ZitaoTech/9981_BLE_USB_Keyboard_Pro/Gallery/Foto1.jpg

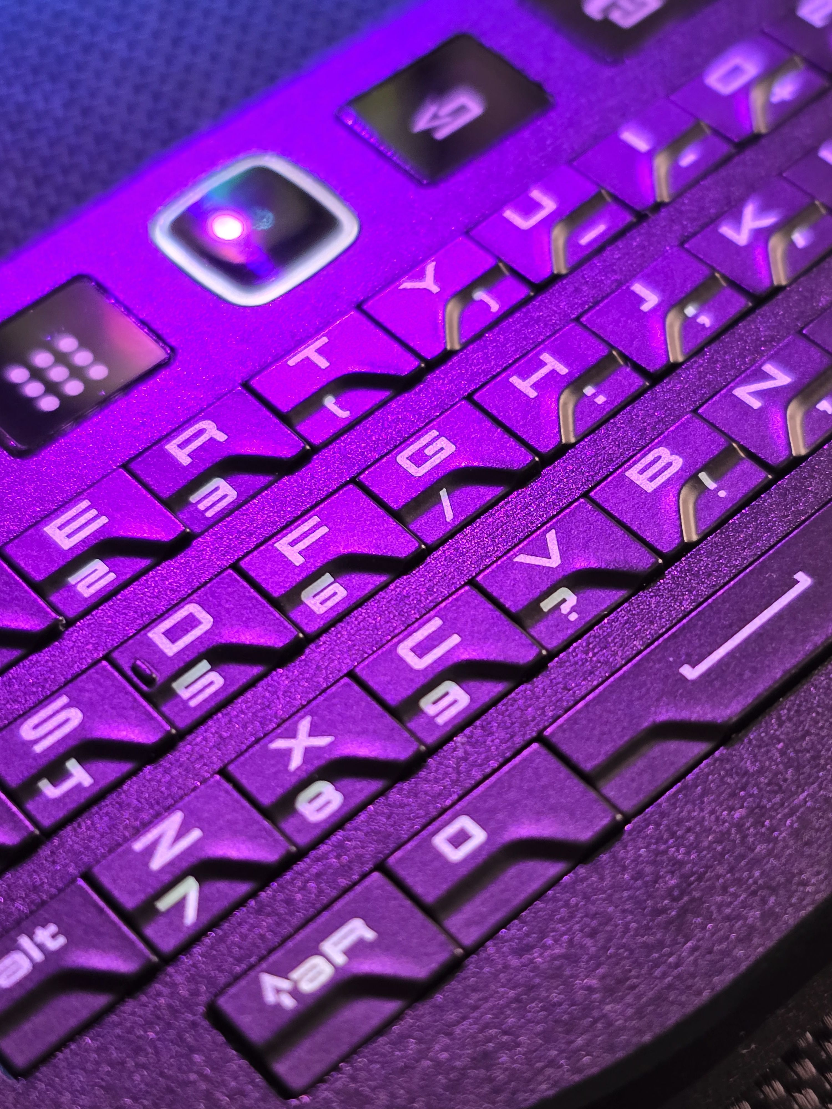
Gallery/Foto1.jpg
