ZitaoTech/9981_BLE_USB_Keyboard_Pro/Gallery/Foto3.jpg

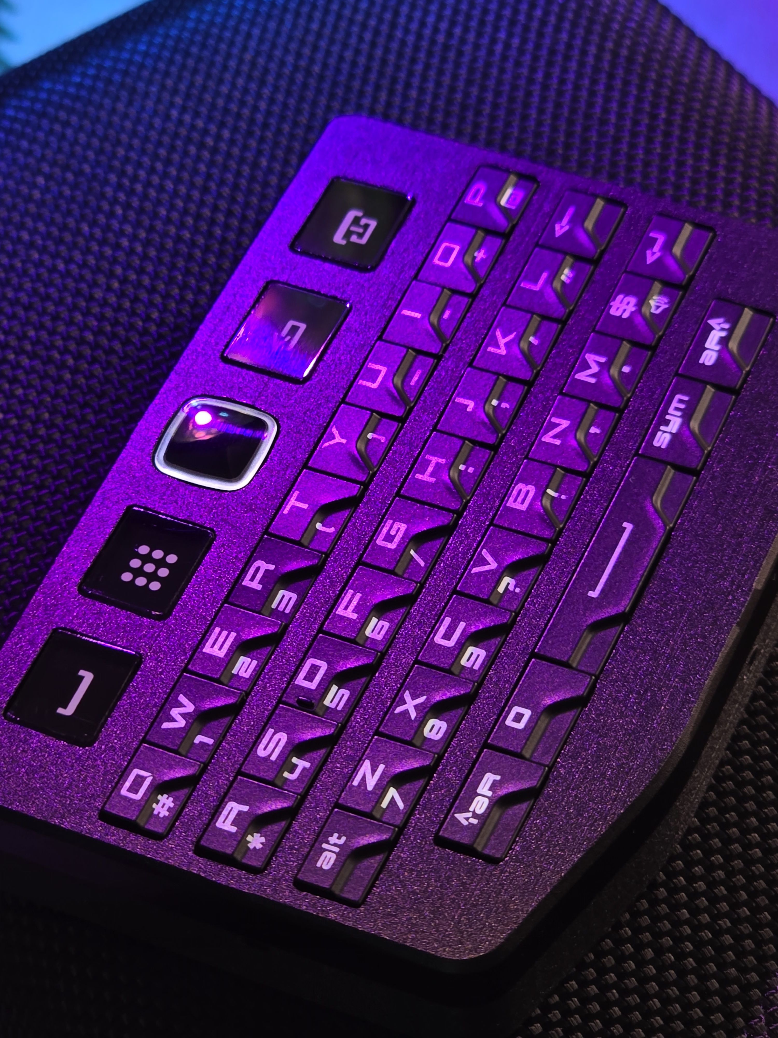
Gallery/Foto3.jpg
