ZitaoTech/9981_BLE_USB_Keyboard_Pro/Gallery/Foto4.jpg

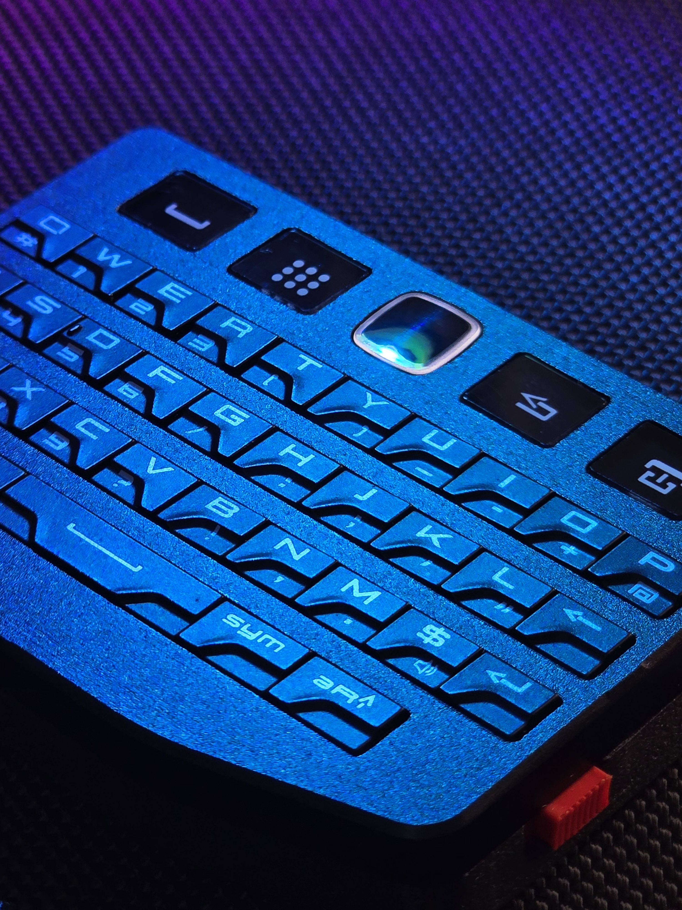
Gallery/Foto4.jpg
