ZitaoTech/9981_BLE_USB_Keyboard_Pro/Gallery/Foto6.jpg

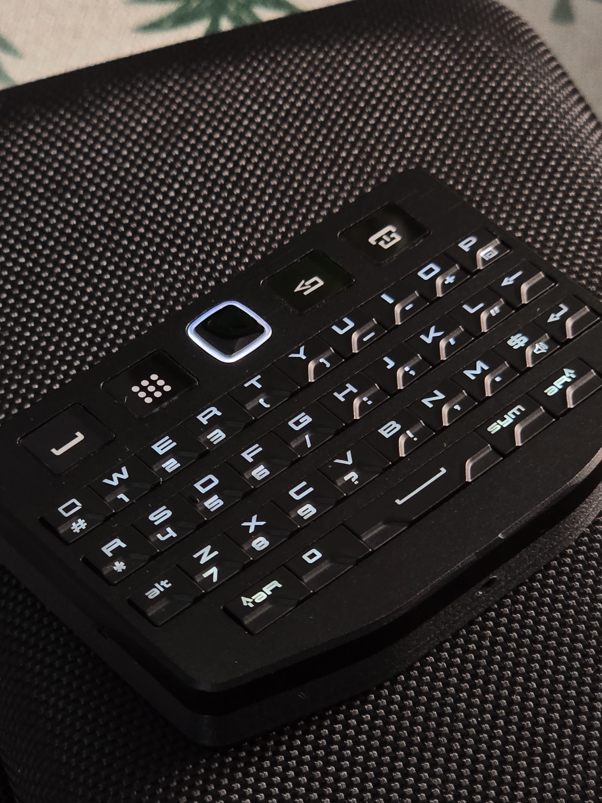
Gallery/Foto6.jpg
