ZitaoTech/9981_BLE_USB_Keyboard_Pro/Gallery/Foto7.jpg

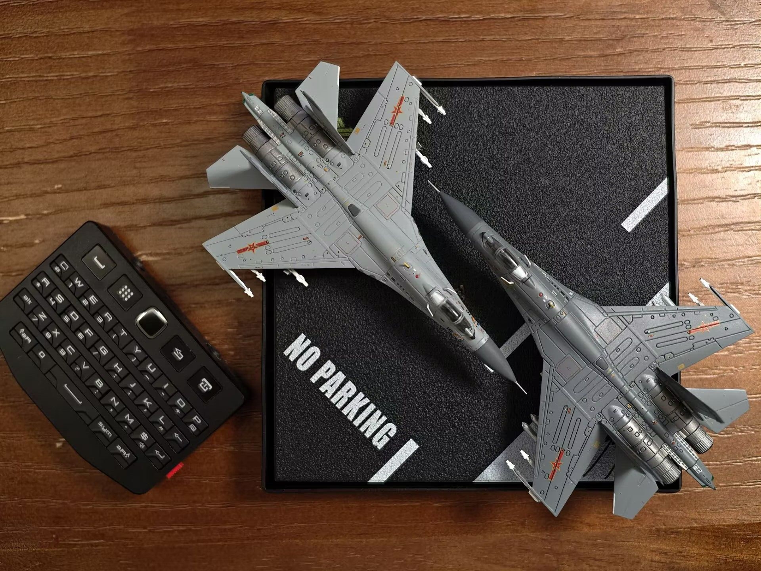
Gallery/Foto7.jpg
