ZitaoTech/9981_BLE_USB_Keyboard_Pro/Mechnical drawing/9981_PRO_dimension.png

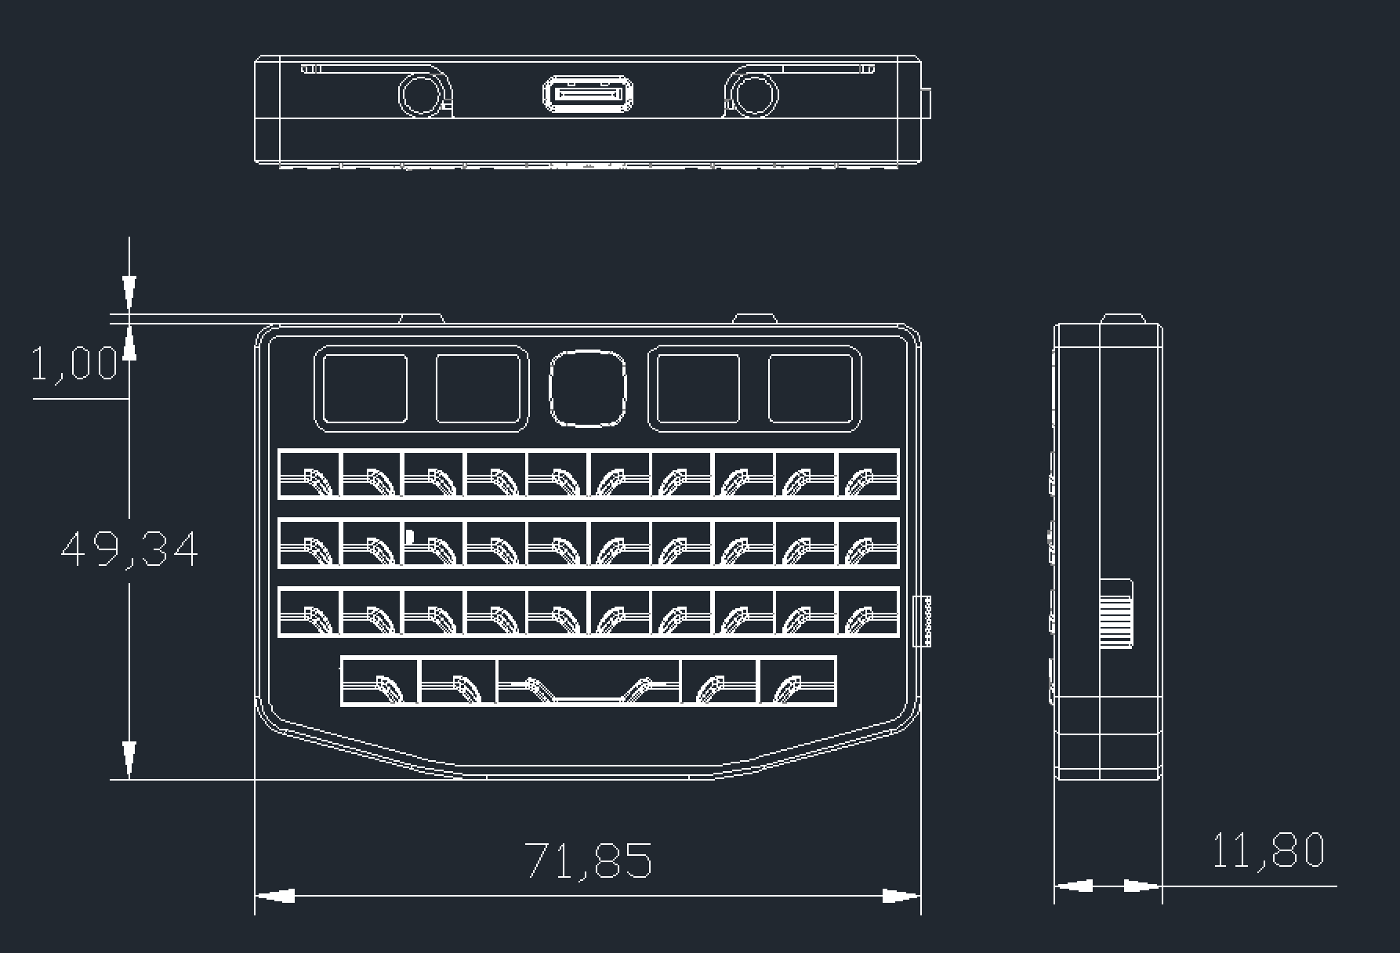
Mechnical drawing/9981_PRO_dimension.png
